xcd0/fennel/arm_split/q/keyboards/kinesis/alvicstep/docs/kicad/kinesis.sch

## KiCad design arm_split/q/keyboards/kinesis/alvicstep/docs/kicad/kinesis.sch (2020-03-29)

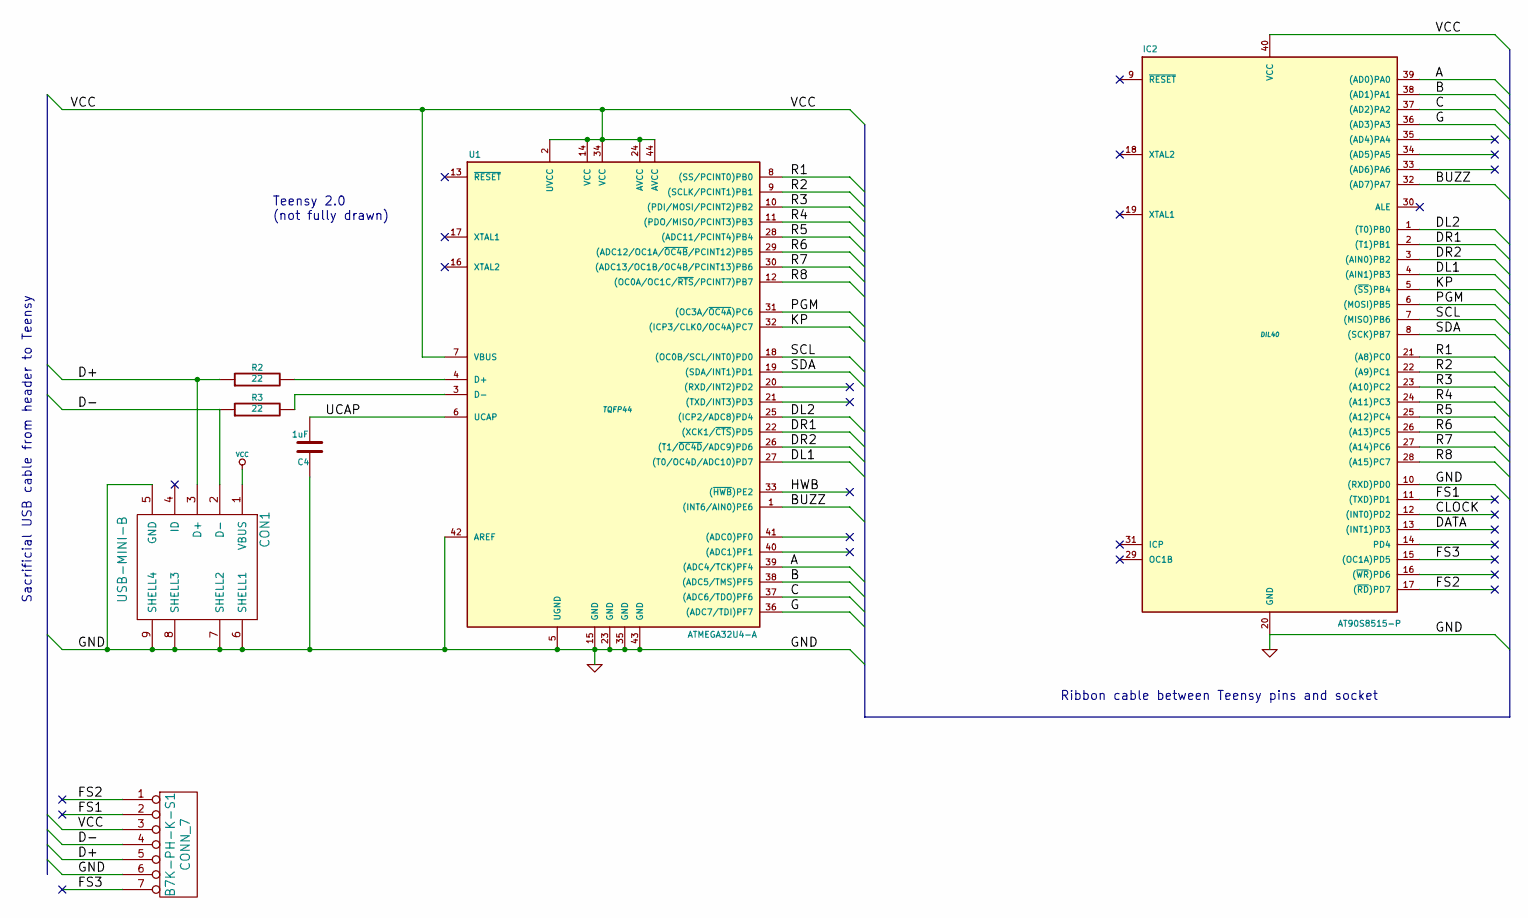
[picture p24: schematic kinesis.sch]

Parts:
B7K-PH-K-S1: CONN_7
C4: 1uF
CON1: USB-MINI-B
IC2: AT90S8515-P; DIL40
R2, R3: 22
U1: ATMEGA32U4-A; TQFP44

Connections:
A: IC2.39 ((AD0)PA0), U1.39 ((ADC4/TCK)PF4)
B: IC2.38 ((AD1)PA1), U1.38 ((ADC5/TMS)PF5)
BUZZ: IC2.32 ((AD7)PA7), U1.1 ((INT6/AIN0)PE6)
C: IC2.37 ((AD2)PA2), U1.37 ((ADC6/TDO)PF6)
CLOCK: IC2.12 ((INT0)PD2)
D+: B7K-PH-K-S1.5, CON1.3 (D+), R2.1
D-: B7K-PH-K-S1.4, CON1.2 (D-), R3.1
DATA: IC2.13 ((INT1)PD3)
DL1: IC2.4 ((AIN1)PB3), U1.27 ((T0/OC4D/ADC10)PD7)
DL2: IC2.1 ((T0)PB0), U1.25 ((ICP2/ADC8)PD4)
DR1: IC2.2 ((T1)PB1), U1.22 ((XCK1/~CTS~)PD5)
DR2: IC2.3 ((AIN0)PB2), U1.26 ((T1/~OC4D~/ADC9)PD6)
FS1: B7K-PH-K-S1.2, IC2.11 ((TXD)PD1)
FS2: B7K-PH-K-S1.1, IC2.17 ((~RD~)PD7)
FS3: B7K-PH-K-S1.7, IC2.15 ((OC1A)PD5)
G: IC2.36 ((AD3)PA3), U1.36 ((ADC7/TDI)PF7)
GND: B7K-PH-K-S1.6, C4.1, CON1.5 (GND), CON1.6 (SHELL1), CON1.7 (SHELL2), CON1.8 (SHELL3), CON1.9 (SHELL4), IC2.10 ((RXD)PD0), IC2.20 (GND), U1.5 (UGND), U1.15 (GND), U1.23 (GND), U1.35 (GND), U1.42 (AREF), U1.43 (GND)
HWB: U1.33 ((~HWB~)PE2)
KP: IC2.5 ((~SS~)PB4), U1.32 ((ICP3/CLK0/OC4A)PC7)
unnamed: R2.2, U1.4 (D+)
unnamed: R3.2, U1.3 (D-)
PGM: IC2.6 ((MOSI)PB5), U1.31 ((OC3A/~OC4A~)PC6)
R1: IC2.21 ((A8)PC0), U1.8 ((SS/PCINT0)PB0)
R2: IC2.22 ((A9)PC1), U1.9 ((SCLK/PCINT1)PB1)
R3: IC2.23 ((A10)PC2), U1.10 ((PDI/MOSI/PCINT2)PB2)
R4: IC2.24 ((A11)PC3), U1.11 ((PDO/MISO/PCINT3)PB3)
R5: IC2.25 ((A12)PC4), U1.28 ((ADC11/PCINT4)PB4)
R6: IC2.26 ((A13)PC5), U1.29 ((ADC12/OC1A/~OC4B~/PCINT12)PB5)
R7: IC2.27 ((A14)PC6), U1.30 ((ADC13/OC1B/OC4B/PCINT13)PB6)
R8: IC2.28 ((A15)PC7), U1.12 ((OC0A/OC1C/~RTS~/PCINT7)PB7)
SCL: IC2.7 ((MISO)PB6), U1.18 ((OC0B/SCL/INT0)PD0)
SDA: IC2.8 ((SCK)PB7), U1.19 ((SDA/INT1)PD1)
UCAP: C4.2, U1.6 (UCAP)
VCC: B7K-PH-K-S1.3, CON1.1 (VBUS), IC2.40 (VCC), U1.2 (UVCC), U1.7 (VBUS), U1.14 (VCC), U1.24 (AVCC), U1.34 (VCC), U1.44 (AVCC)

Notes on the sheet:
Teensy 2.0 (not fully drawn)
Sacrificial USB cable from header to Teensy
Ribbon cable between Teensy pins and socket
